attexx/rfm9x_breakout_board/KiCAD/rev.1/images/01.png

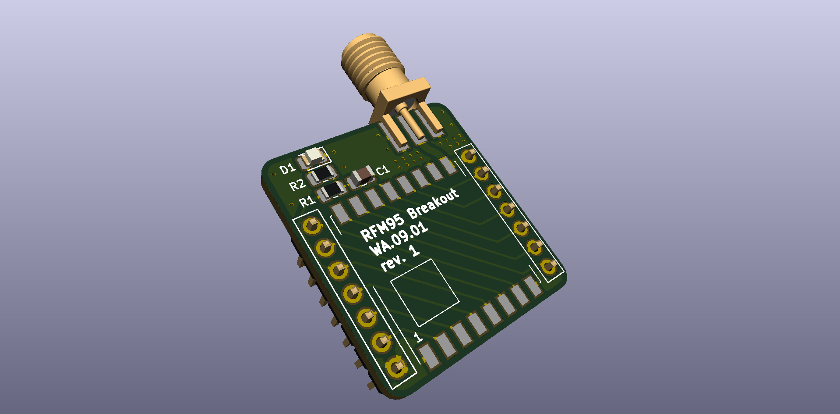
KiCAD/rev.1/images/01.png
