attexx/rfm9x_breakout_board/KiCAD/rev.1/images/bottom.svg.s.png

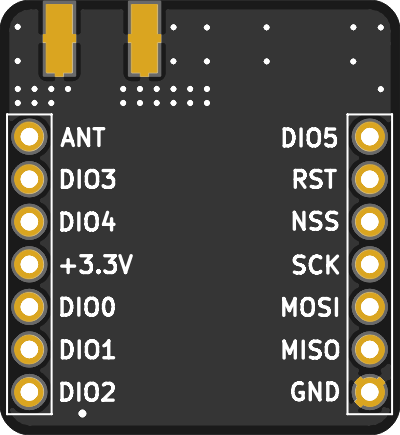
KiCAD/rev.1/images/bottom.svg.s.png
